wachcio/meteo_vue/public/assets/slider/IMG_20180407_161528834.jpg

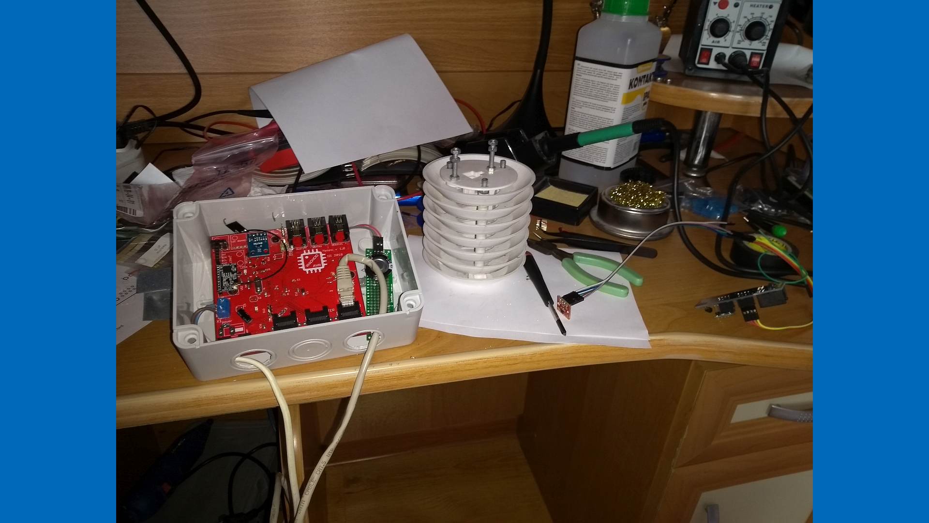
public/assets/slider/IMG_20180407_161528834.jpg
