wachcio/meteo_vue/public/assets/slider/IMG_20180408_112302544.jpg

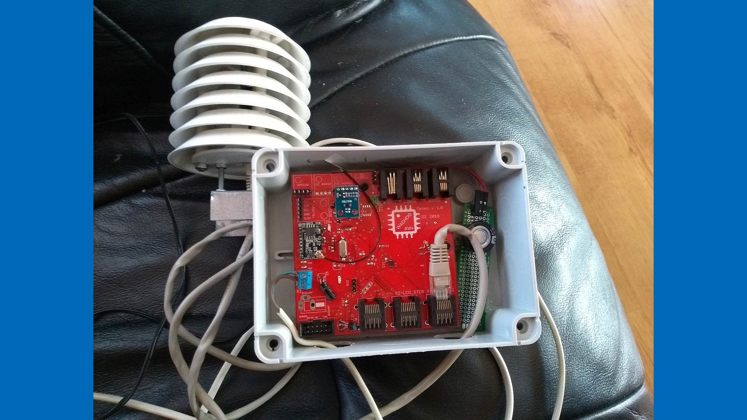
public/assets/slider/IMG_20180408_112302544.jpg
