wachcio/meteo_vue/public/assets/slider/IMG_20190104_144055.jpg

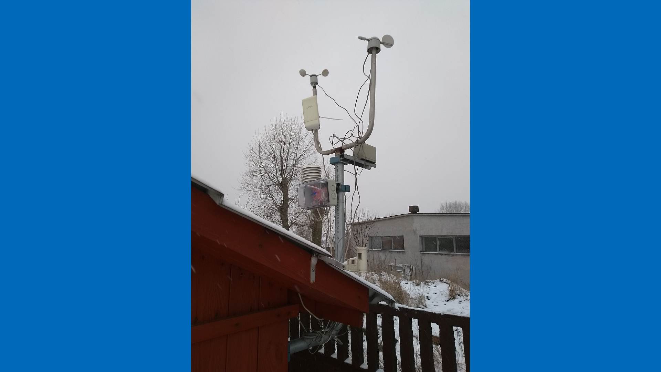
public/assets/slider/IMG_20190104_144055.jpg
